SAIRISAN123/ClickGuard/Circuit/Circuit Proteus.bmp

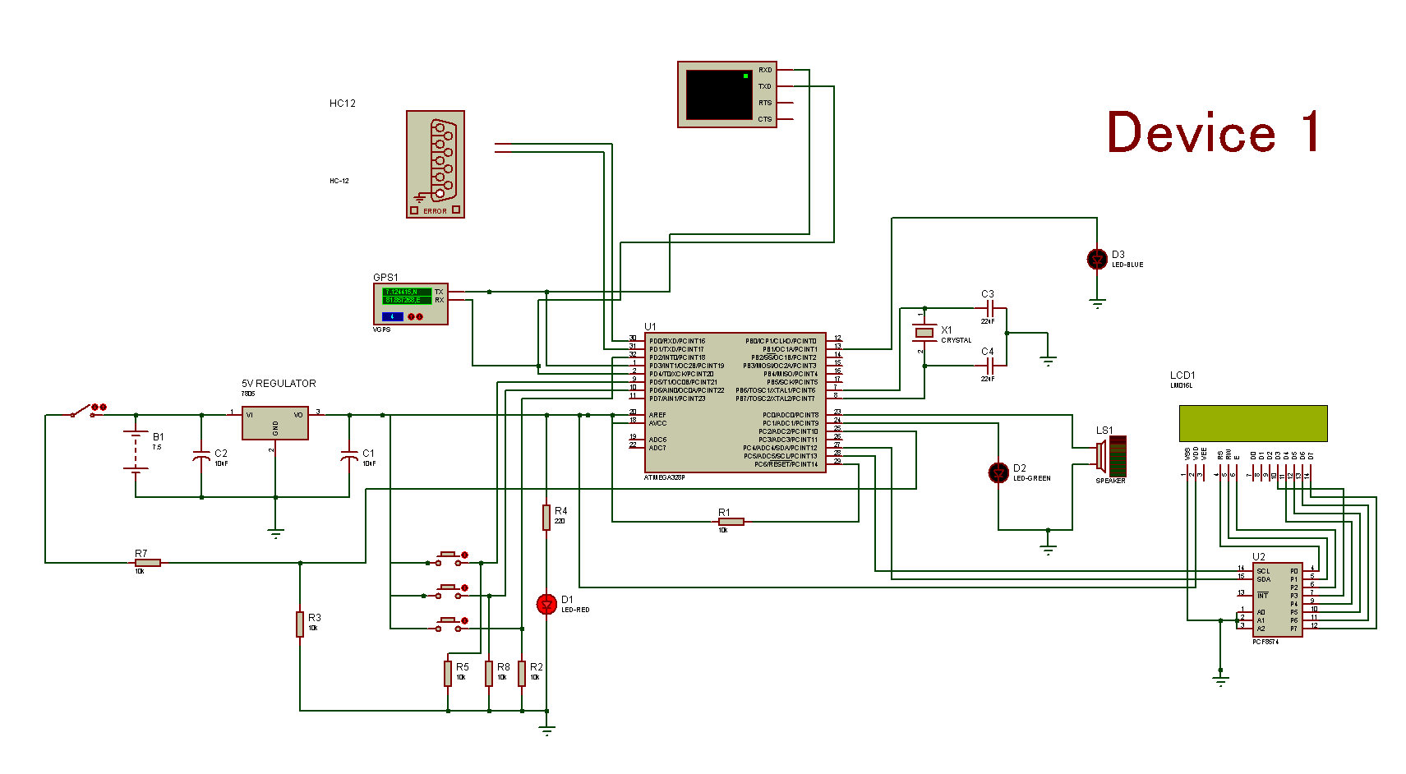
Circuit/Circuit Proteus.bmp
