SAIRISAN123/ClickGuard/Final Design/1.JPG

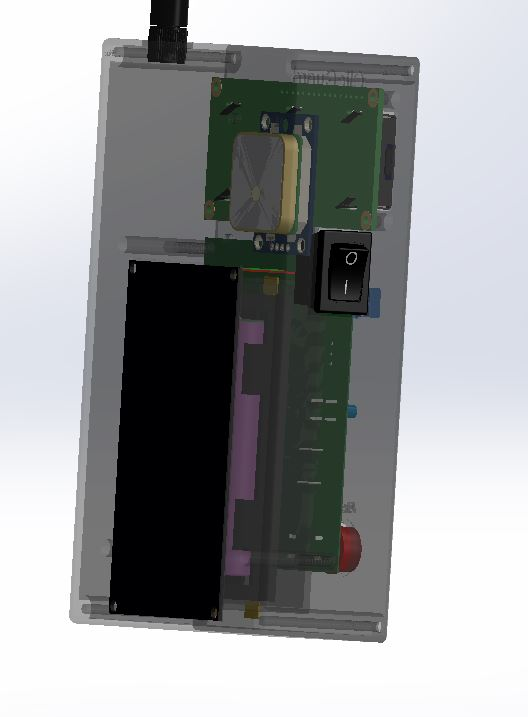
Final Design/1.JPG
