SAIRISAN123/ClickGuard/Images/0.JPG

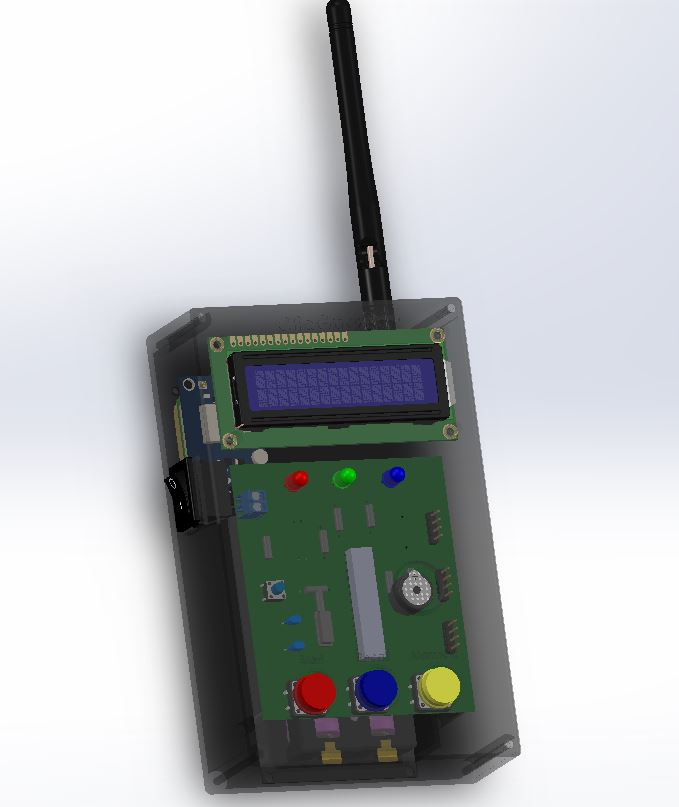
Images/0.JPG
