SAIRISAN123/ClickGuard/Images/1.jpg

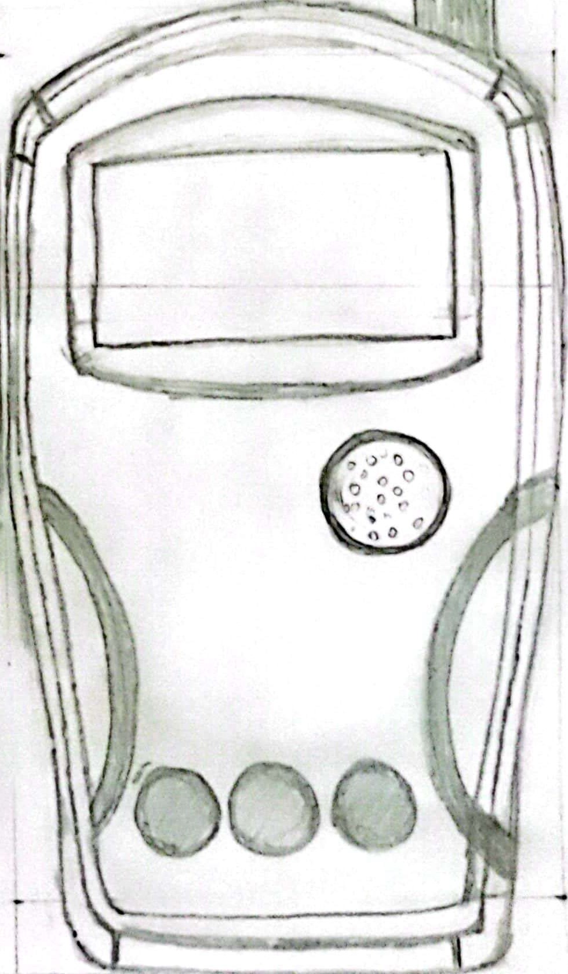
Images/1.jpg
