SAIRISAN123/ClickGuard/Images/2.jpg

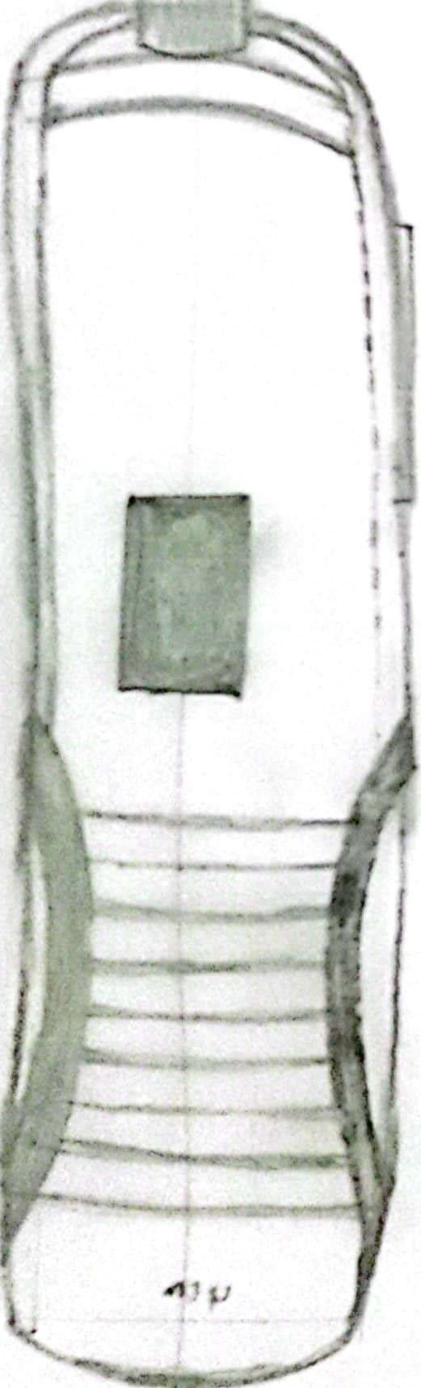
Images/2.jpg
