SAIRISAN123/ClickGuard/Images/3.JPG

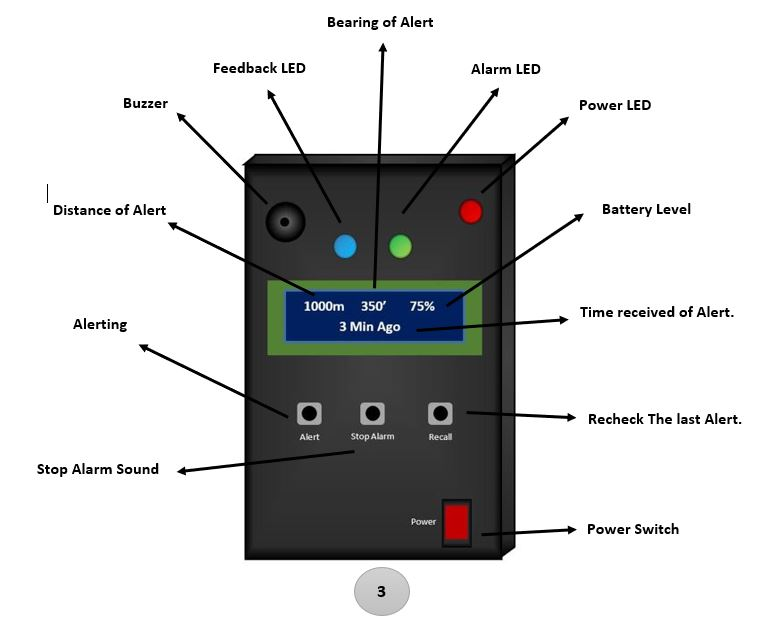
Images/3.JPG
