SAIRISAN123/ClickGuard/Images/7.JPG

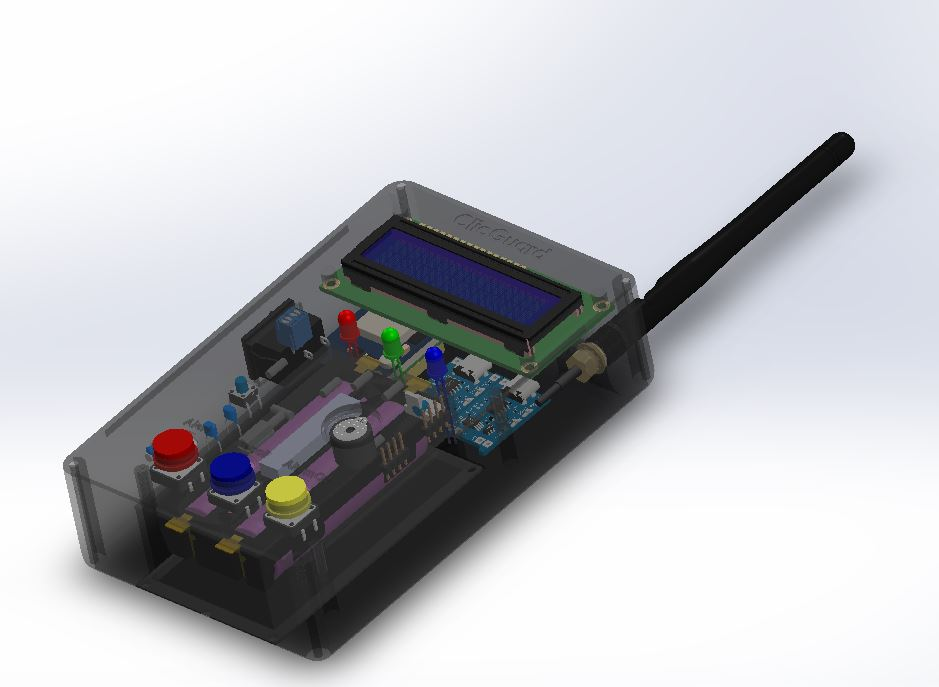
Images/7.JPG
