SAIRISAN123/ClickGuard/Images/black.JPG

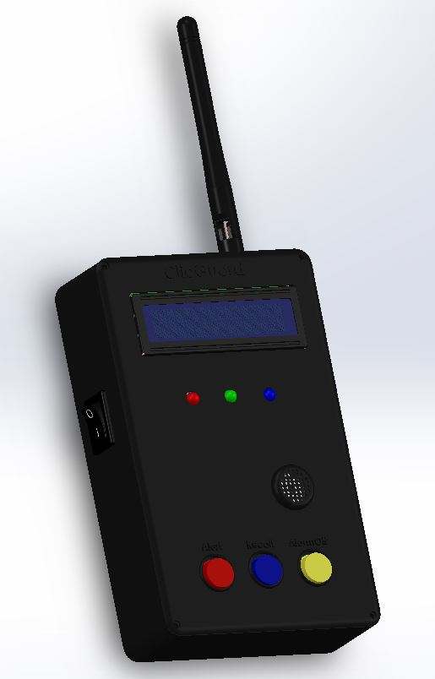
Images/black.JPG
