SAIRISAN123/ClickGuard/Images/CamScanner 05-30-2023 12.14.jpg

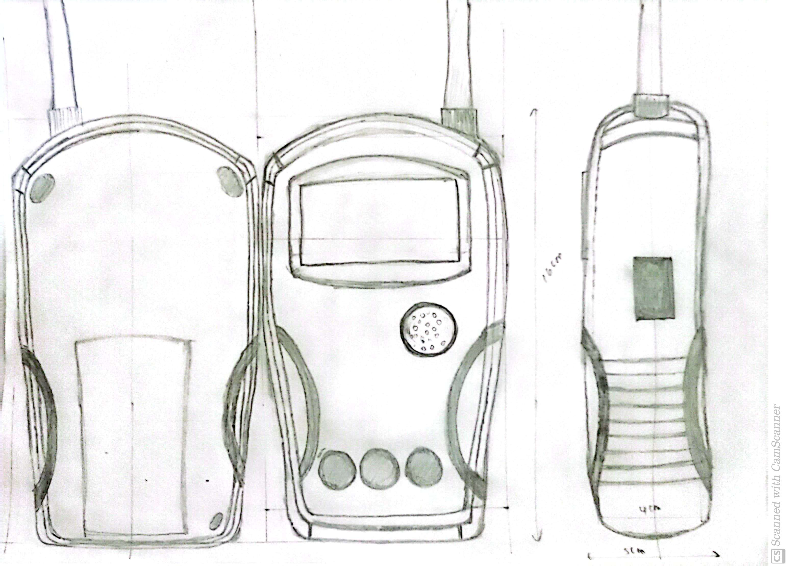
Images/CamScanner 05-30-2023 12.14.jpg
