SAIRISAN123/ClickGuard/Images/Capture.JPG

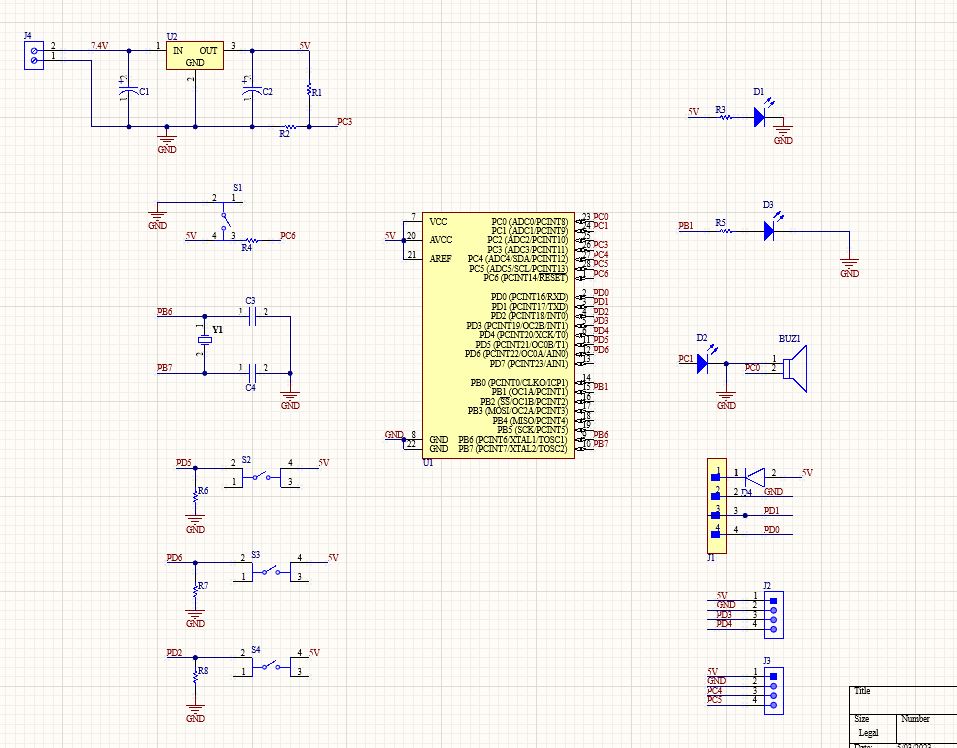
Images/Capture.JPG
