SAIRISAN123/ClickGuard/Images/Cicguard.JPG

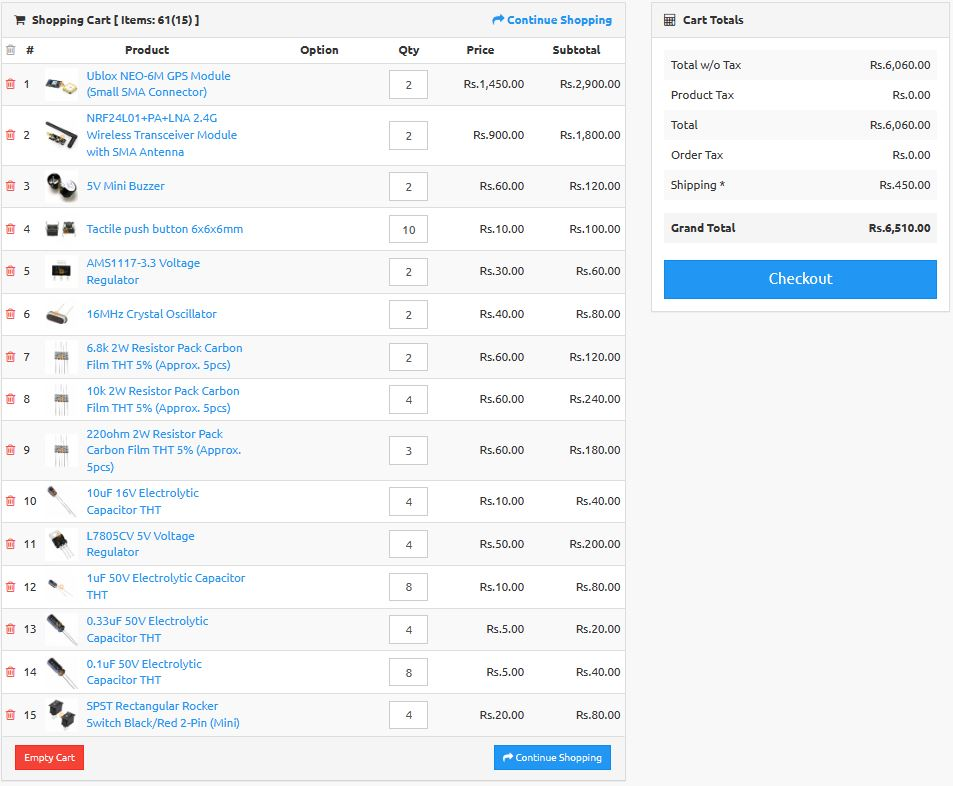
Images/Cicguard.JPG
