SAIRISAN123/ClickGuard/Images/PCB.JPG

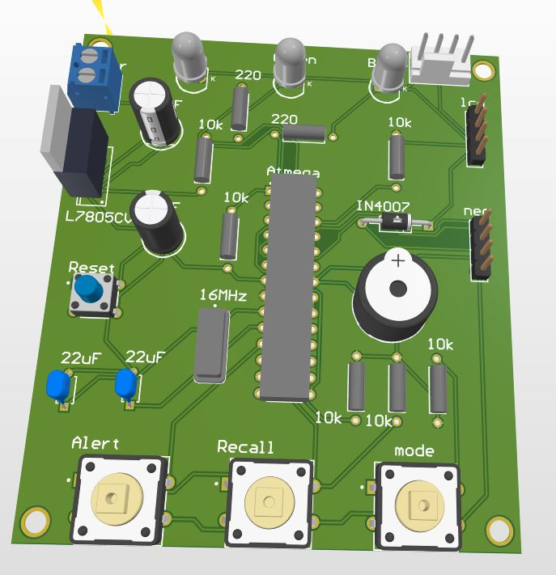
Images/PCB.JPG
