SAIRISAN123/ClickGuard/Images/Xray.JPG

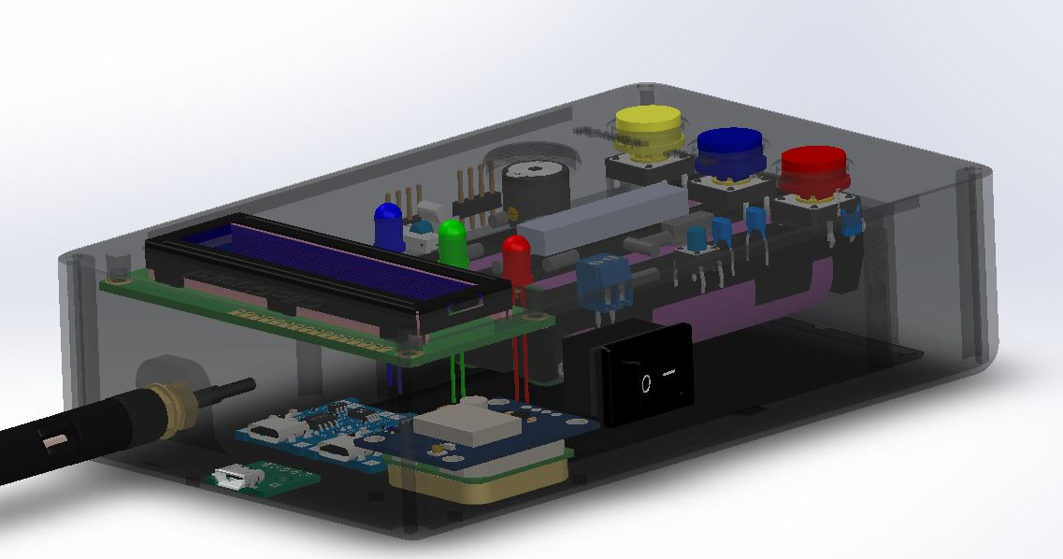
Images/Xray.JPG
